nicotakuya/diy-keypad64/8x8font.h

// 8pixel font by Takuya Matsubara.
PROGMEM const unsigned char font[] = {
0x00,0x00,0x00,0x00,0x00,0x00,0x00,0x00 /*font32*/
,0x18,0x18,0x18,0x18,0x18,0x00,0x18,0x00 /*font33*/
,0x6c,0x6c,0x24,0x48,0x00,0x00,0x00,0x00 /*font34*/
,0x28,0x28,0xfe,0x28,0xfe,0x28,0x28,0x00 /*font35*/
,0x10,0x7e,0x90,0x7c,0x12,0xfc,0x10,0x00 /*font36*/
,0x42,0xa4,0x48,0x10,0x24,0x4a,0x84,0x00 /*font37*/
,0x30,0x48,0x48,0x30,0x4a,0x84,0x7a,0x00 /*font38*/
,0x18,0x18,0x08,0x10,0x00,0x00,0x00,0x00 /*font39*/
,0x18,0x20,0x40,0x40,0x40,0x20,0x18,0x00 /*font40*/
,0x30,0x08,0x04,0x04,0x04,0x08,0x30,0x00 /*font41*/
,0x92,0x54,0x38,0xfe,0x38,0x54,0x92,0x00 /*font42*/
,0x10,0x10,0x10,0xfe,0x10,0x10,0x10,0x00 /*font43*/
,0x00,0x00,0x00,0x00,0x30,0x30,0x60,0x00 /*font44*/
,0x00,0x00,0x00,0xfe,0x00,0x00,0x00,0x00 /*font45*/
,0x00,0x00,0x00,0x00,0x00,0x30,0x30,0x00 /*font46*/
,0x00,0x02,0x04,0x08,0x10,0x20,0x40,0x00 /*font47*/
,0x7c,0x82,0x8a,0x92,0xa2,0x82,0x7c,0x00 /*font48*/
,0x10,0x30,0x10,0x10,0x10,0x10,0x38,0x00 /*font49*/
,0xfc,0x02,0x02,0x3c,0x40,0x80,0xfe,0x00 /*font50*/
,0xfc,0x02,0x02,0xfc,0x02,0x02,0xfc,0x00 /*font51*/
,0x18,0x28,0x48,0x88,0xfe,0x08,0x08,0x00 /*font52*/
,0xfe,0x80,0x80,0xfc,0x02,0x02,0xfc,0x00 /*font53*/
,0x7e,0x80,0x80,0xfc,0x82,0x82,0x7c,0x00 /*font54*/
,0xfe,0x02,0x04,0x08,0x10,0x20,0x40,0x00 /*font55*/
,0x7c,0x82,0x82,0x7c,0x82,0x82,0x7c,0x00 /*font56*/
,0x7c,0x82,0x82,0x7e,0x02,0x02,0xfc,0x00 /*font57*/
,0x30,0x30,0x00,0x00,0x30,0x30,0x00,0x00 /*font58*/
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
,0x08,0x10,0x10,0x20,0x10,0x10,0x08,0x00 /*font123*/
,0x10,0x10,0x10,0x00,0x10,0x10,0x10,0x00 /*font124*/
,0x10,0x08,0x08,0x04,0x08,0x08,0x10,0x00 /*font125*/
,0xfe,0x00,0x00,0x00,0x00,0x00,0x00,0x00 /*font126*/
,0x81,0x42,0x24,0x18,0x18,0x24,0x42,0x81 /*font127*/
};
